yeomansr/cs207-2017-project/img/20170319_104711.jpg

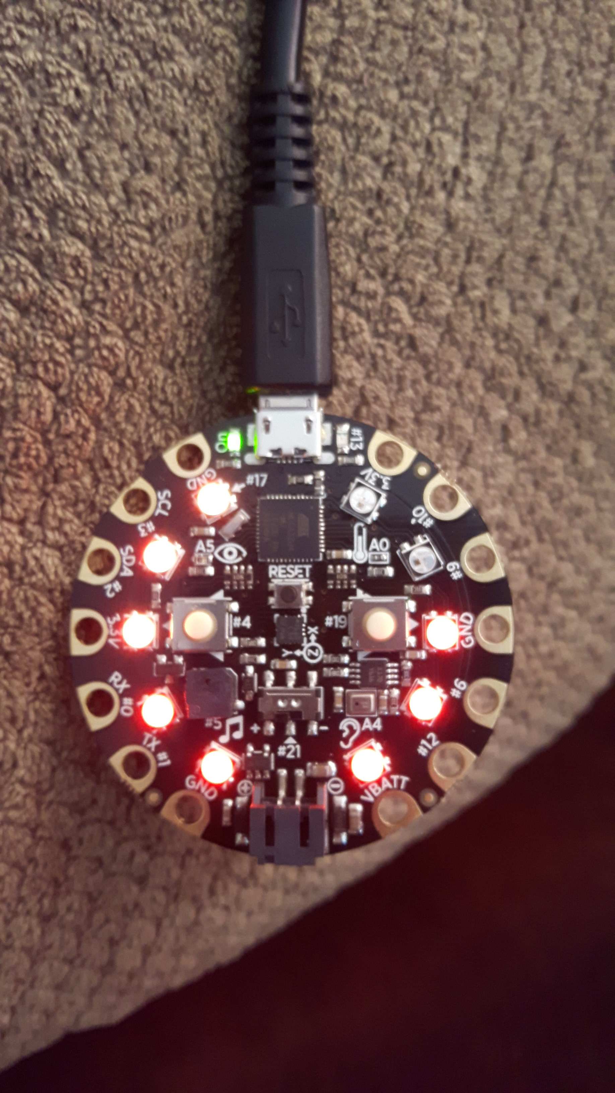
img/20170319_104711.jpg
