yeomansr/cs207-2017-project/img/20170407_160252.jpg

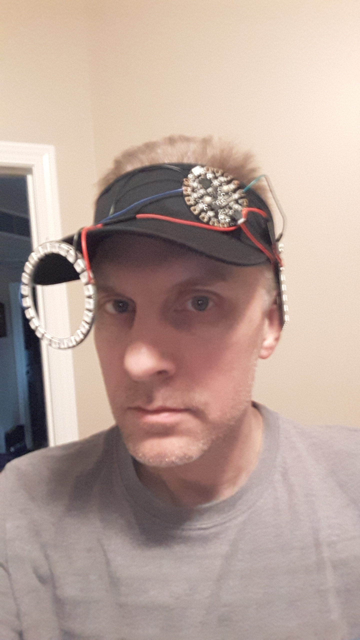
img/20170407_160252.jpg
