yeomansr/cs207-2017-project/img/20170407_160304.jpg

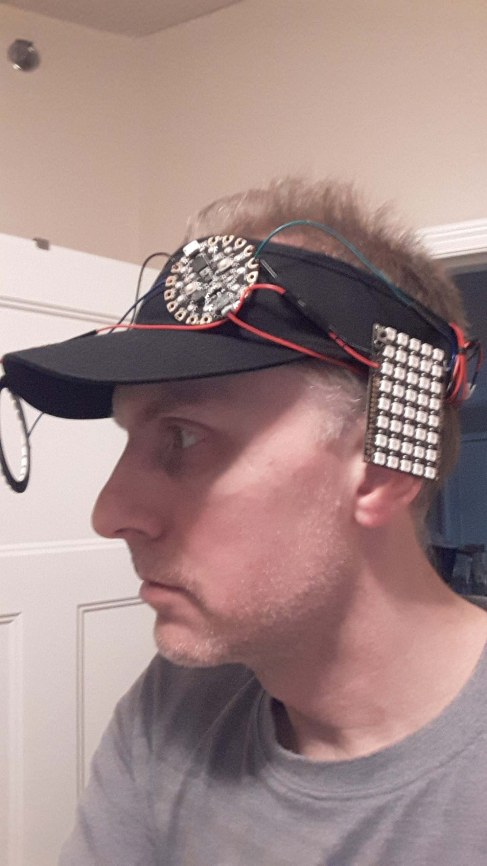
img/20170407_160304.jpg
