yeomansr/cs207-2017-project/img/20170407_160344.jpg

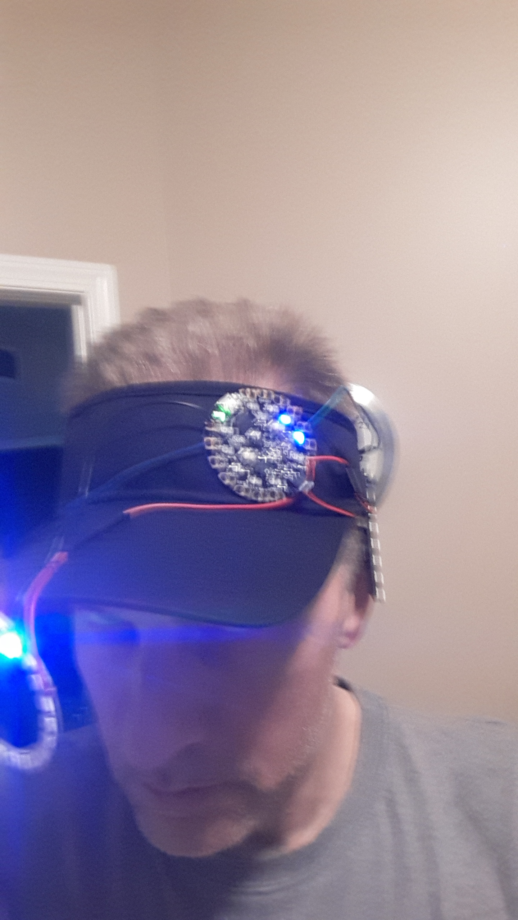
img/20170407_160344.jpg
