yeomansr/cs207-2017-project/img/20170407_160517.jpg

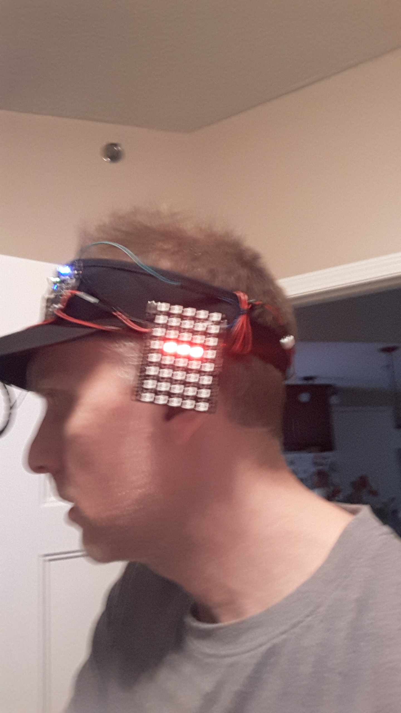
img/20170407_160517.jpg
